merlijn-sebrechts/Splitflaps/documentation/datasheets/schema.png

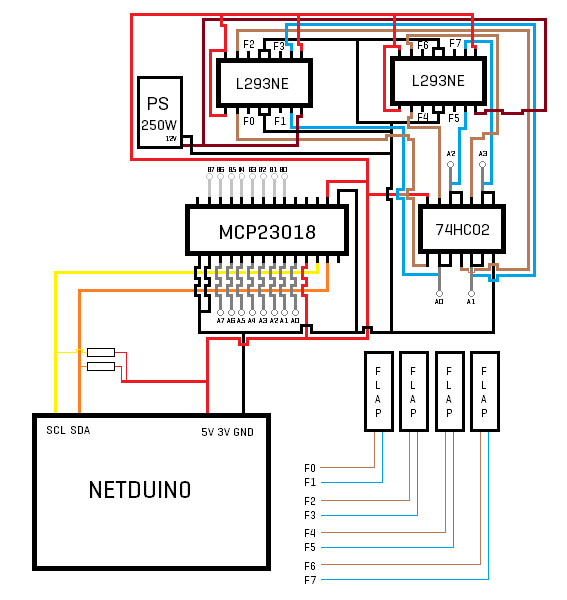
documentation/datasheets/schema.png
