merlijn-sebrechts/Splitflaps/documentation/designs & technical reports/design casing/twitterboard_backplate.jpg

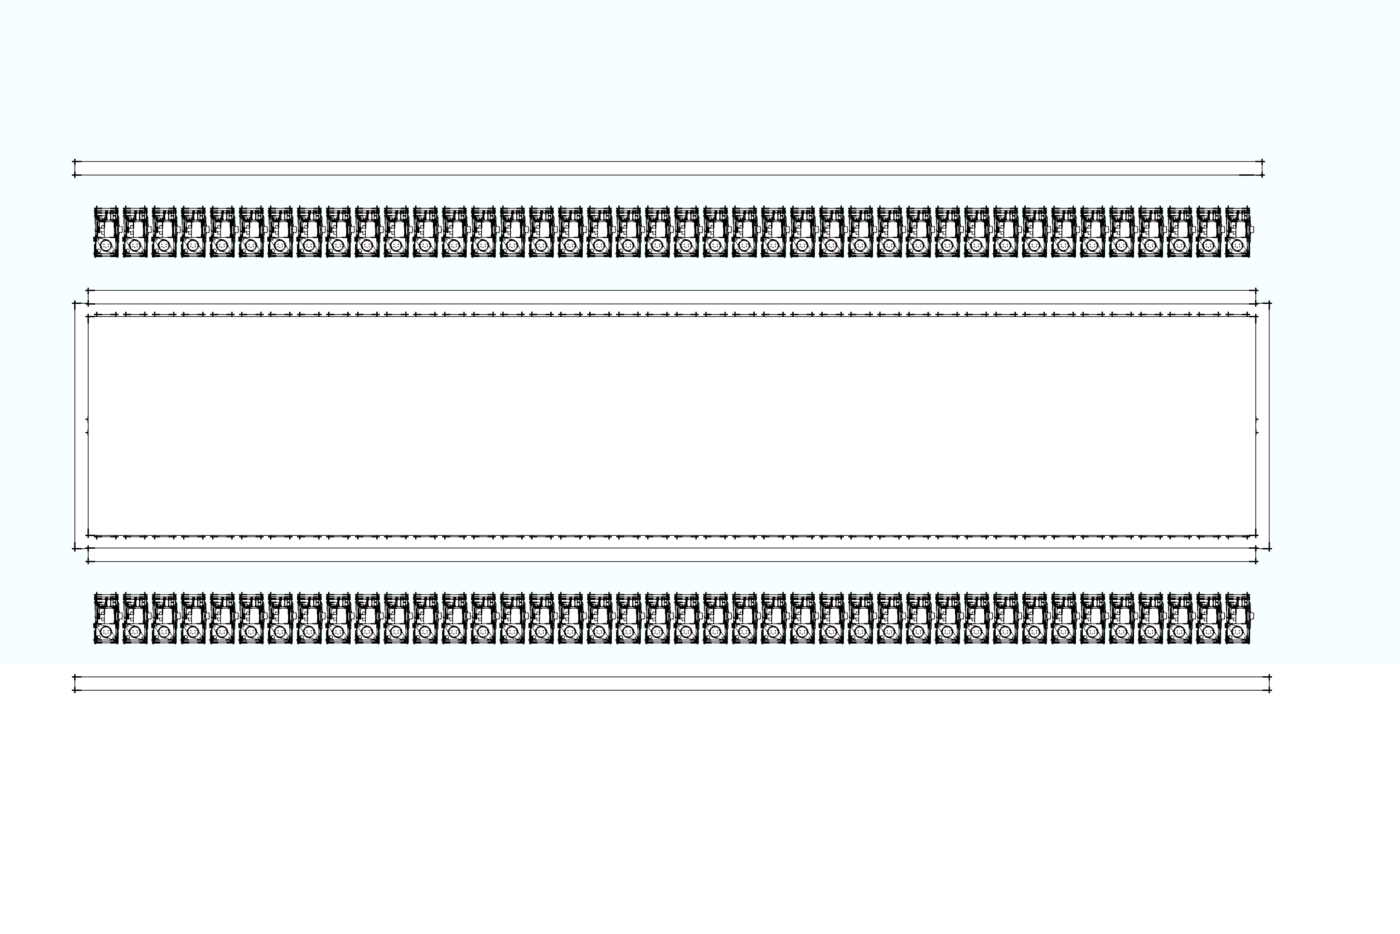
documentation/designs & technical reports/design casing/twitterboard_backplate.jpg
