merlijn-sebrechts/Splitflaps/documentation/designs & technical reports/design casing/twitterboard_elevationwithoutfrontplate.jpg

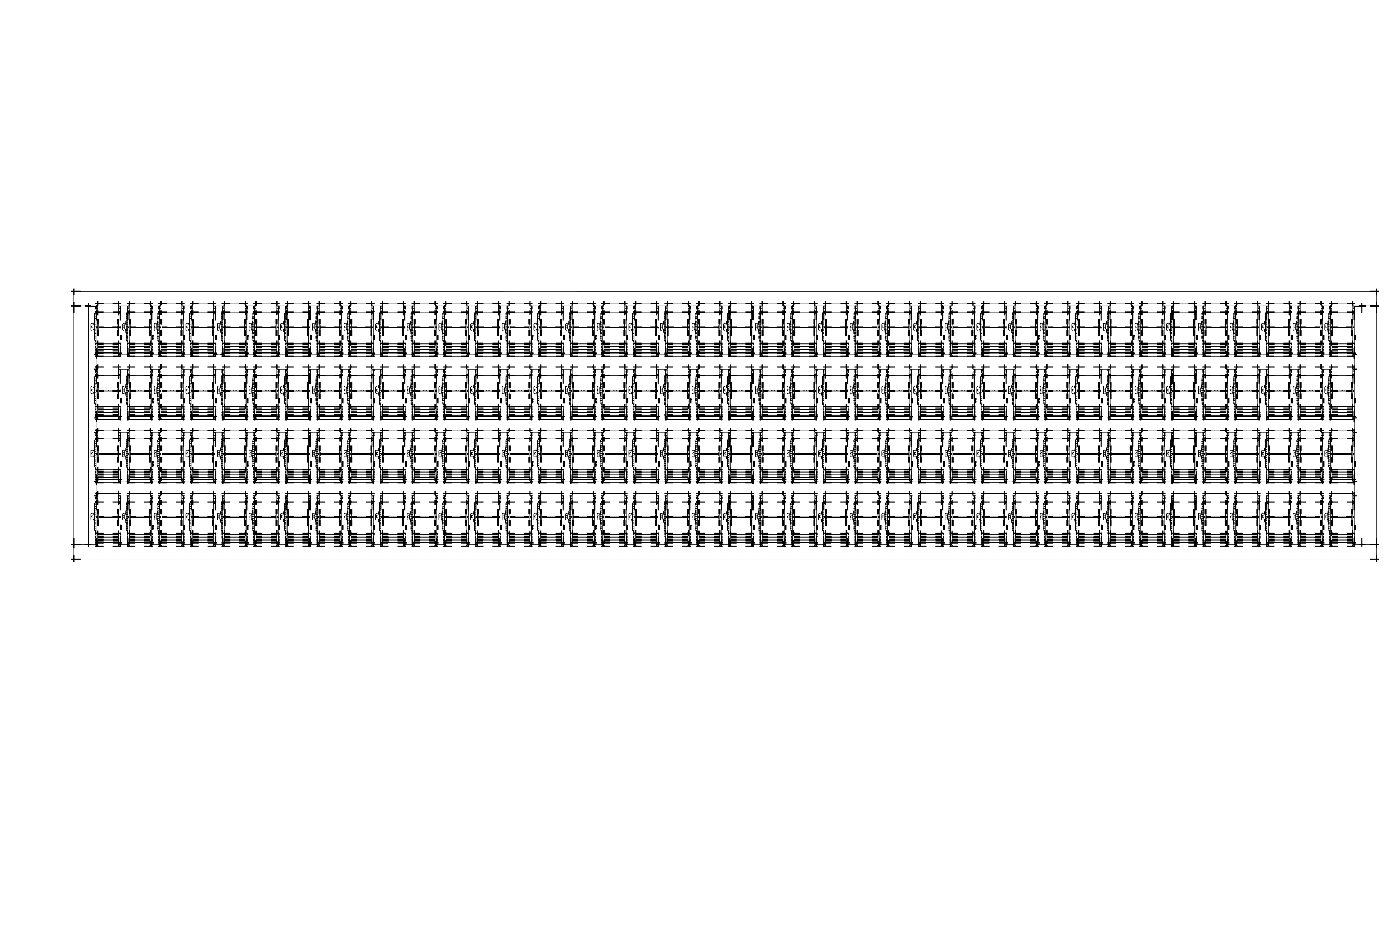
documentation/designs & technical reports/design casing/twitterboard_elevationwithoutfrontplate.jpg
