merlijn-sebrechts/Splitflaps/documentation/designs & technical reports/design casing/twitterboard_frontplate.jpg

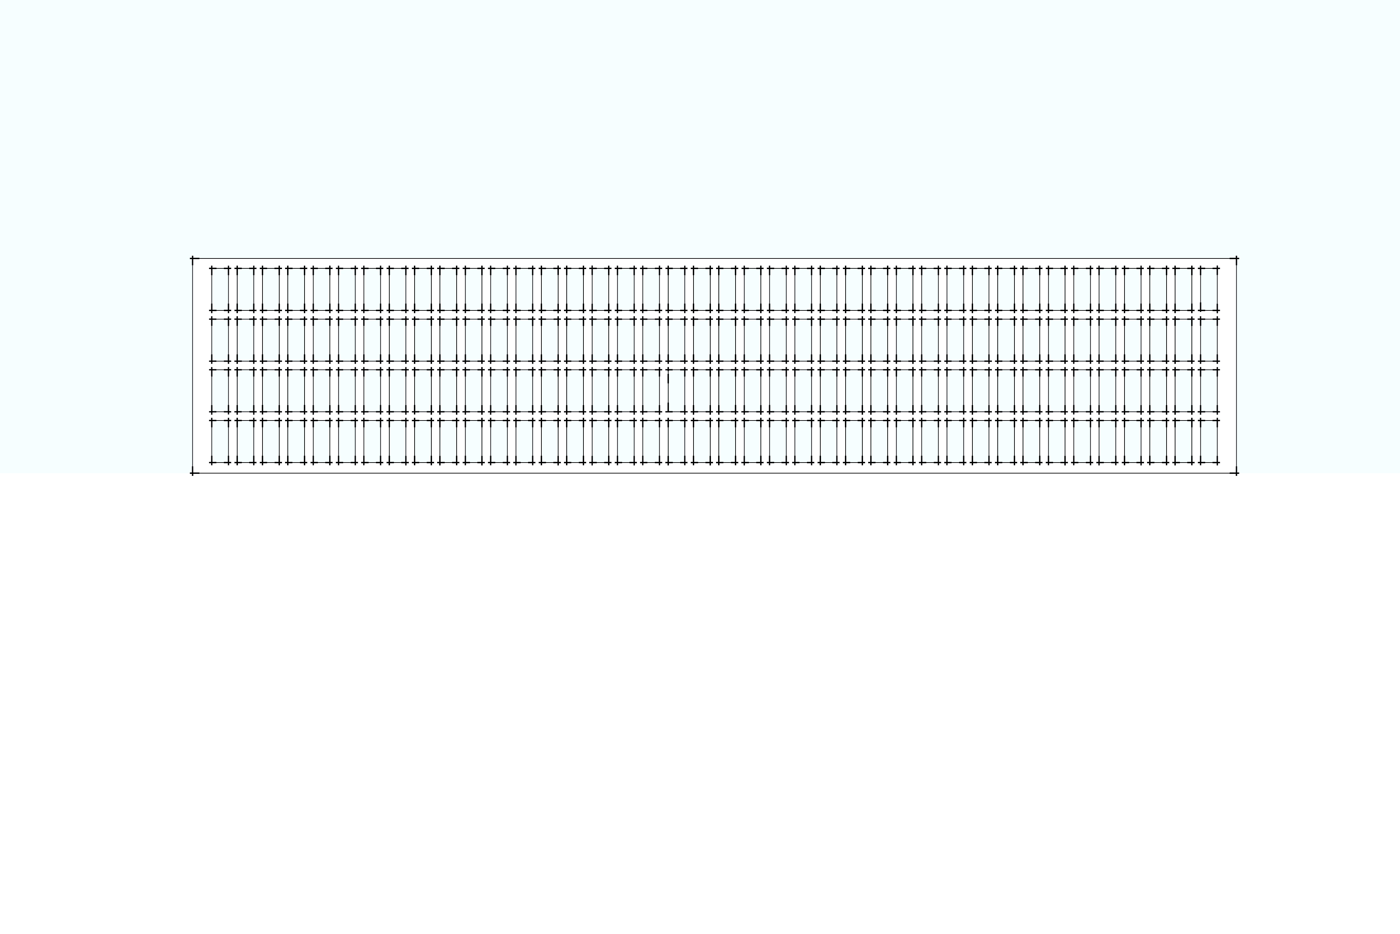
documentation/designs & technical reports/design casing/twitterboard_frontplate.jpg
