merlijn-sebrechts/Splitflaps/documentation/designs & technical reports/design casing/twitterboard_sideelevation.jpg

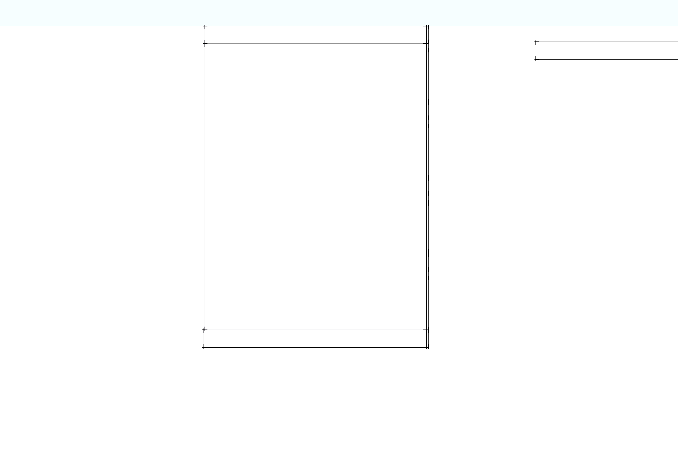
documentation/designs & technical reports/design casing/twitterboard_sideelevation.jpg
