merlijn-sebrechts/Splitflaps/documentation/designs & technical reports/soldeerboard.png

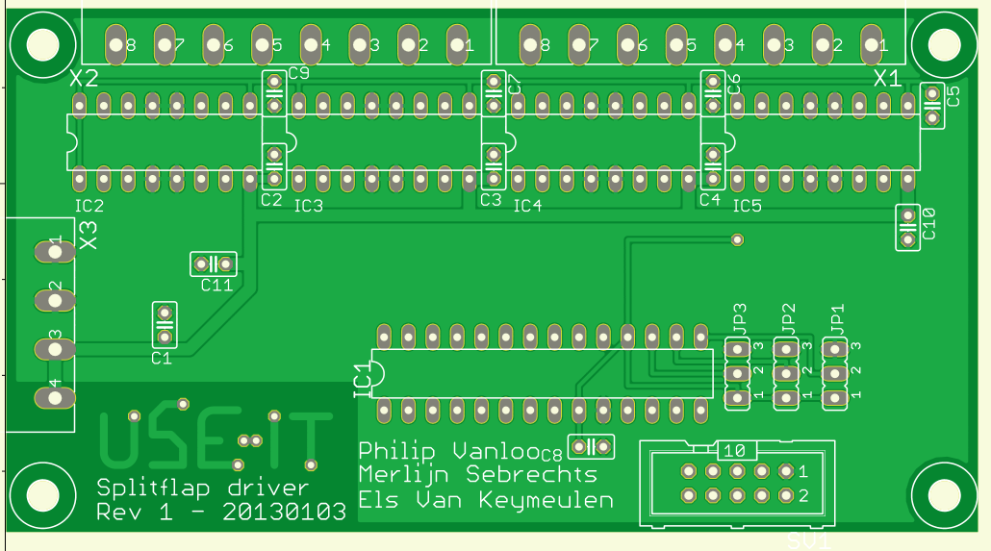
documentation/designs & technical reports/soldeerboard.png
