merlijn-sebrechts/Splitflaps/documentation/designs & technical reports/Sturing van de splitflaps/eendraad klad.jpg

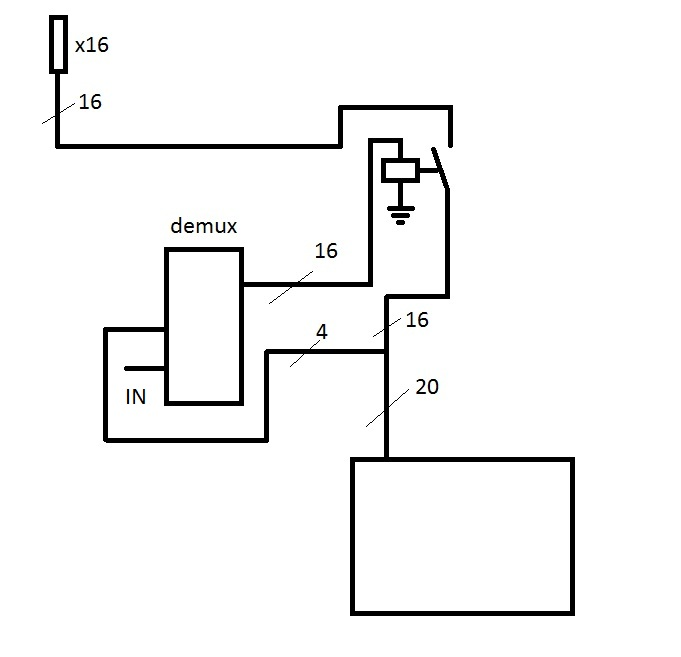
documentation/designs & technical reports/Sturing van de splitflaps/eendraad klad.jpg
