merlijn-sebrechts/Splitflaps/documentation/frontend.png

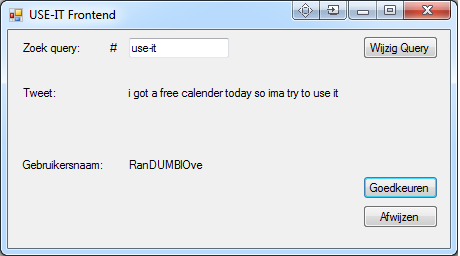
documentation/frontend.png
