merlijn-sebrechts/Splitflaps/documentation/Media/2012-03-01 15.24.06.jpg

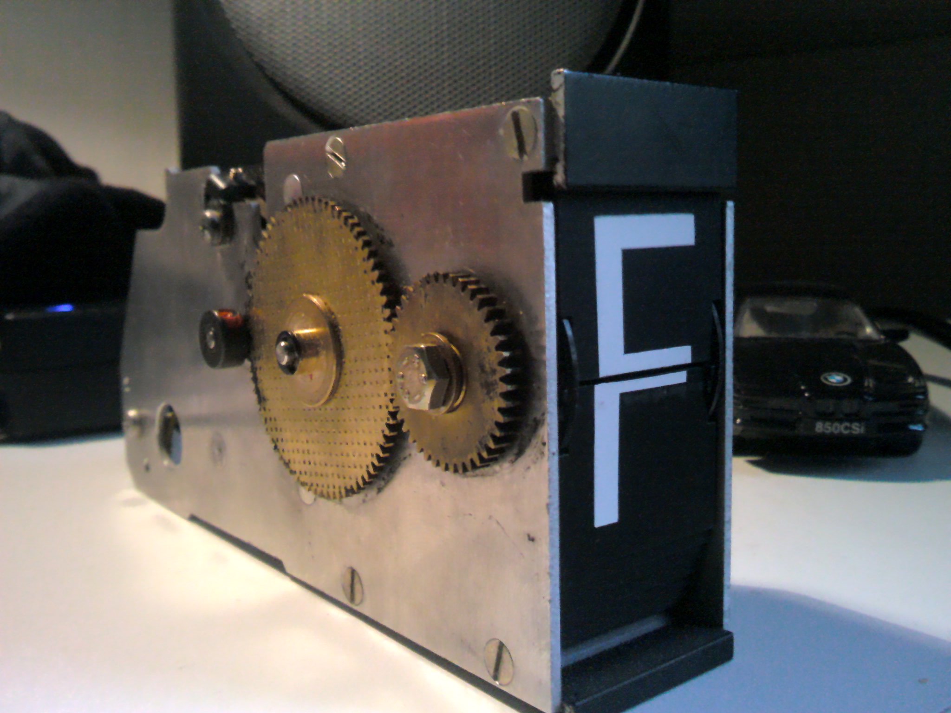
documentation/Media/2012-03-01 15.24.06.jpg
