merlijn-sebrechts/Splitflaps/documentation/Media/2012-03-01 15.25.54.jpg

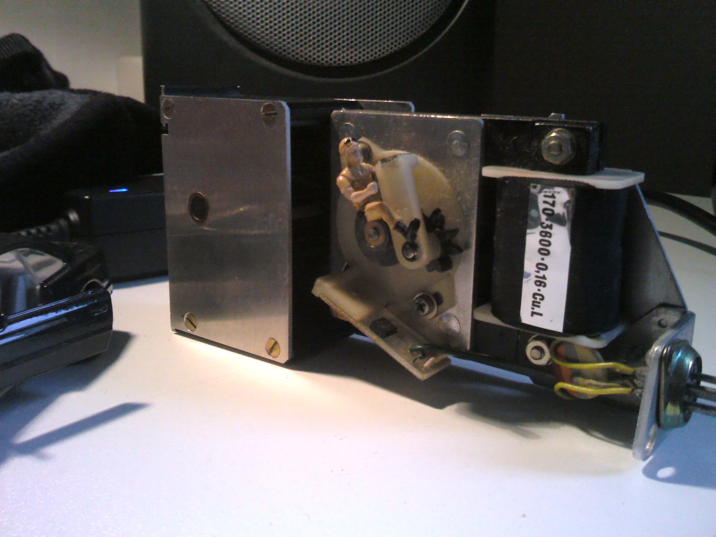
documentation/Media/2012-03-01 15.25.54.jpg
