merlijn-sebrechts/Splitflaps/documentation/Media/2012-03-01 15.26.38.jpg

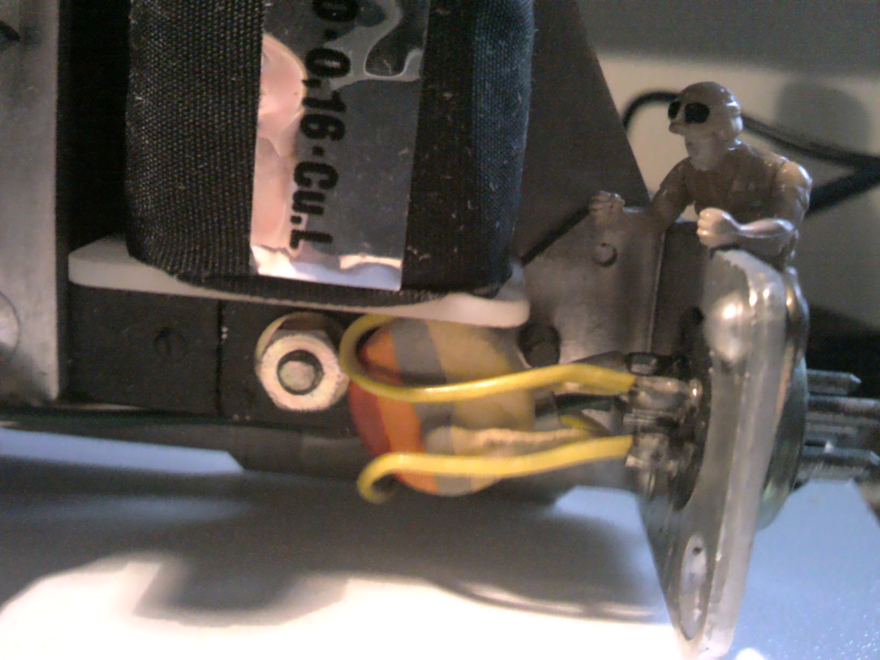
documentation/Media/2012-03-01 15.26.38.jpg
