merlijn-sebrechts/Splitflaps/documentation/Media/2012-03-26 11.21.38.jpg

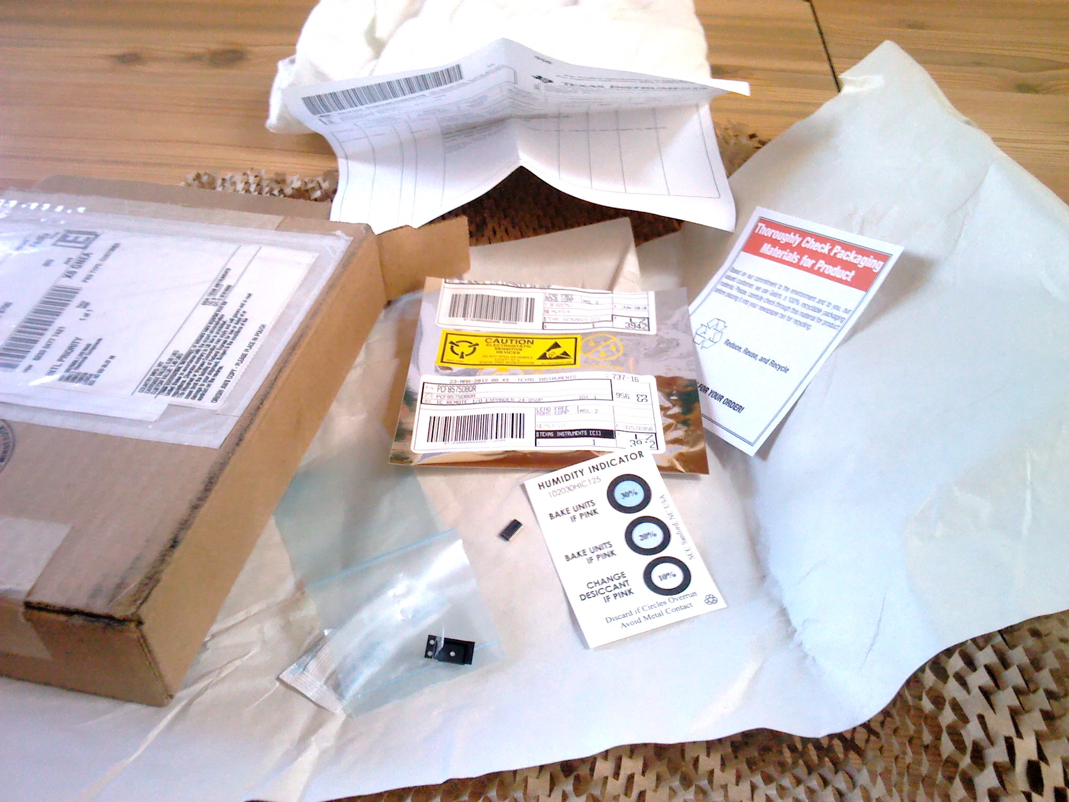
documentation/Media/2012-03-26 11.21.38.jpg
