merlijn-sebrechts/Splitflaps/documentation/Media/2012-05-13 12.06.36.jpg

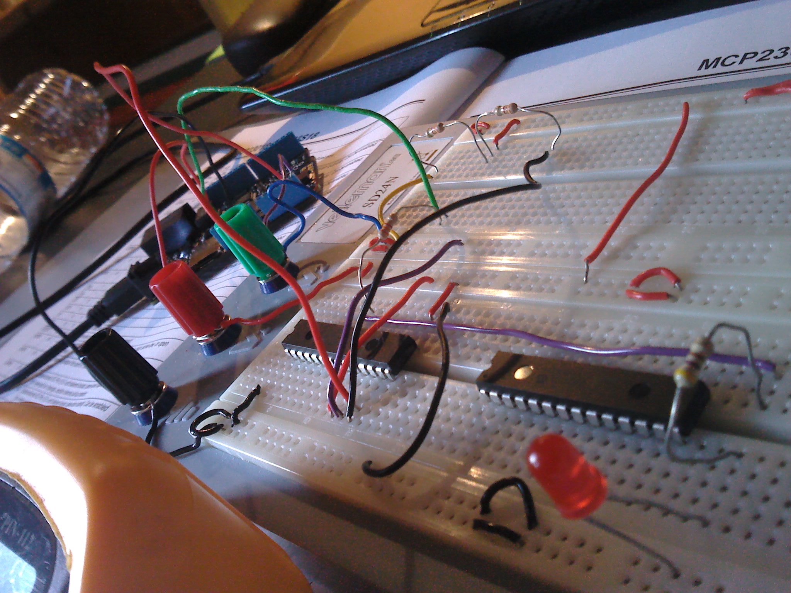
documentation/Media/2012-05-13 12.06.36.jpg
