merlijn-sebrechts/Splitflaps/documentation/Media/2012-05-24 22.02.43.jpg

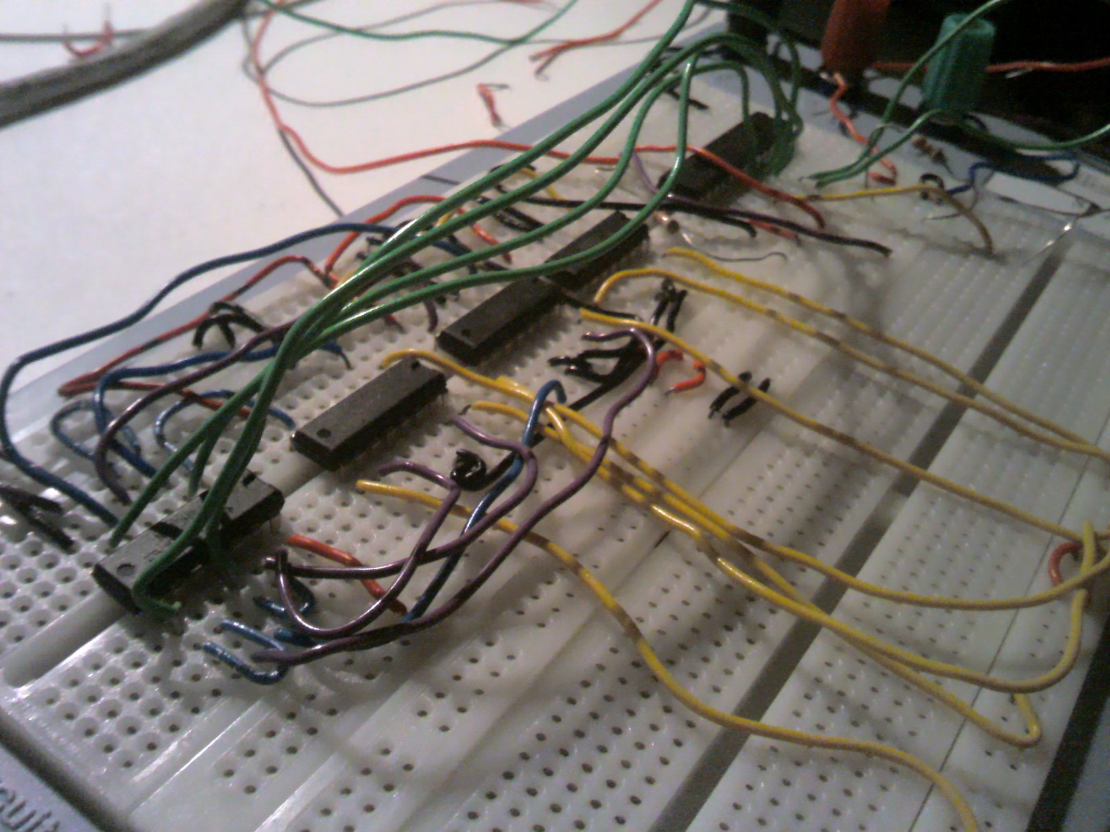
documentation/Media/2012-05-24 22.02.43.jpg
