merlijn-sebrechts/Splitflaps/documentation/Media/2012-10-18 19.46.36.jpg

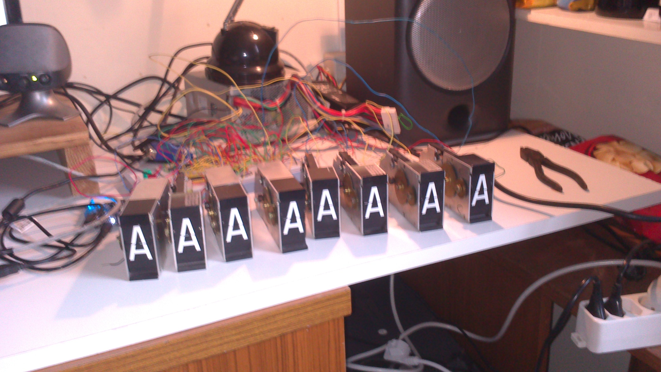
documentation/Media/2012-10-18 19.46.36.jpg
