merlijn-sebrechts/Splitflaps/documentation/Media/2013-10-26 10.34.53.jpg

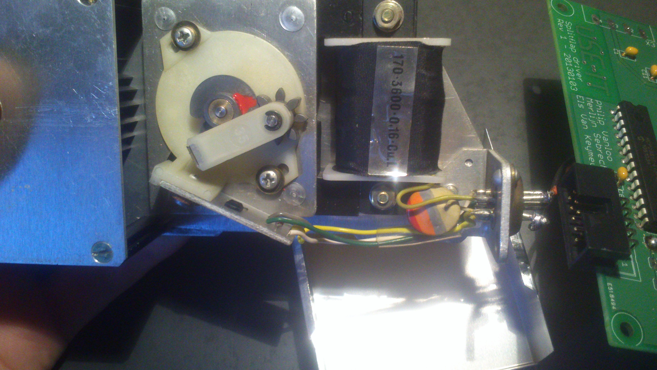
documentation/Media/2013-10-26 10.34.53.jpg
