merlijn-sebrechts/Splitflaps/documentation/Media/2013-10-26 10.35.50.jpg

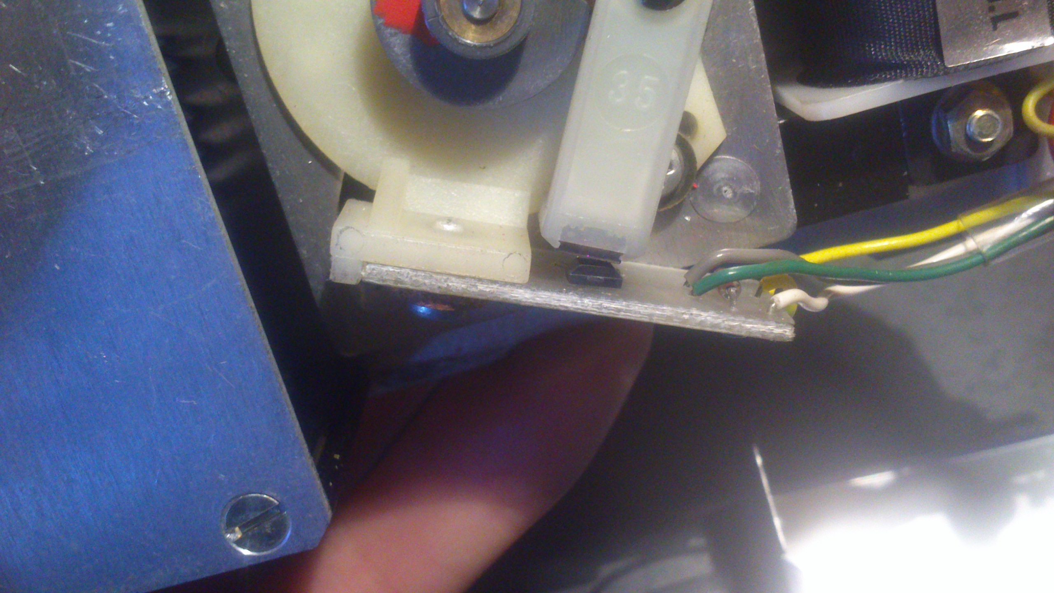
documentation/Media/2013-10-26 10.35.50.jpg
