merlijn-sebrechts/Splitflaps/documentation/Media/2013-10-26 10.36.17.jpg

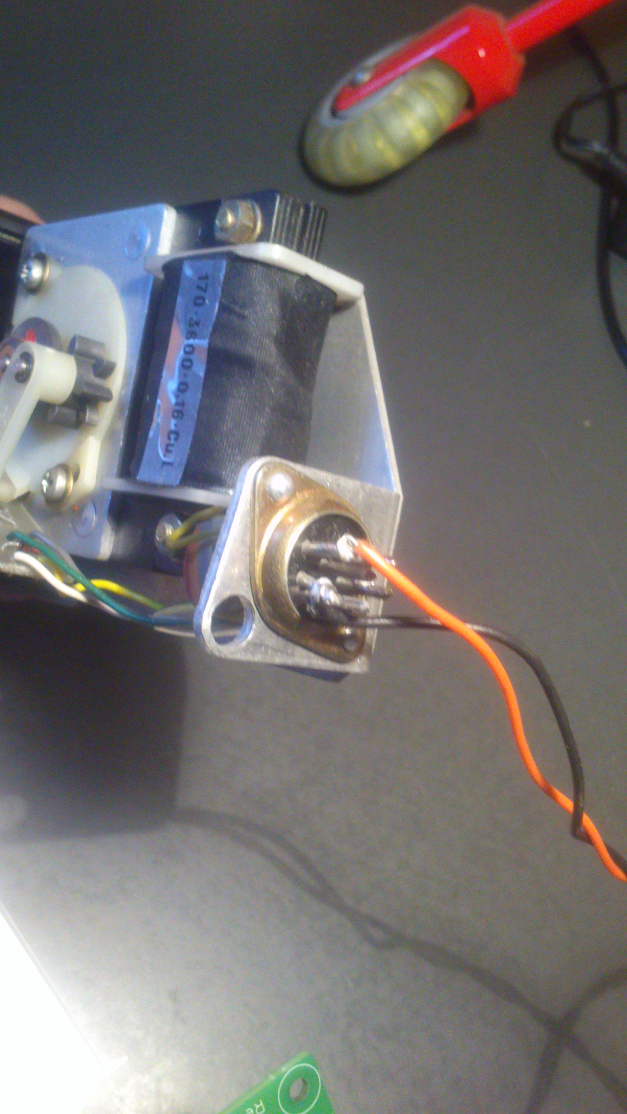
documentation/Media/2013-10-26 10.36.17.jpg
