merlijn-sebrechts/Splitflaps/documentation/Media/2013-10-26 10.39.55.jpg

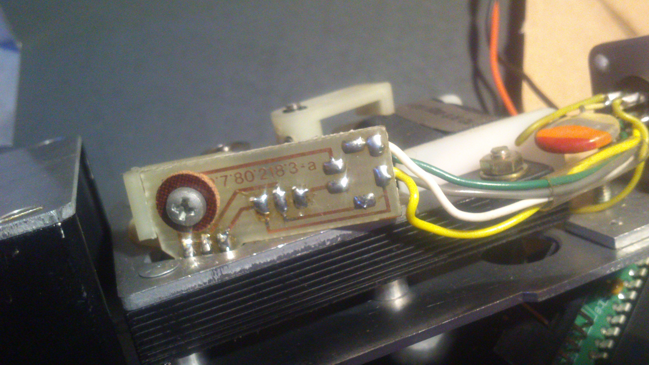
documentation/Media/2013-10-26 10.39.55.jpg
