merlijn-sebrechts/Splitflaps/documentation/Naamloos.png

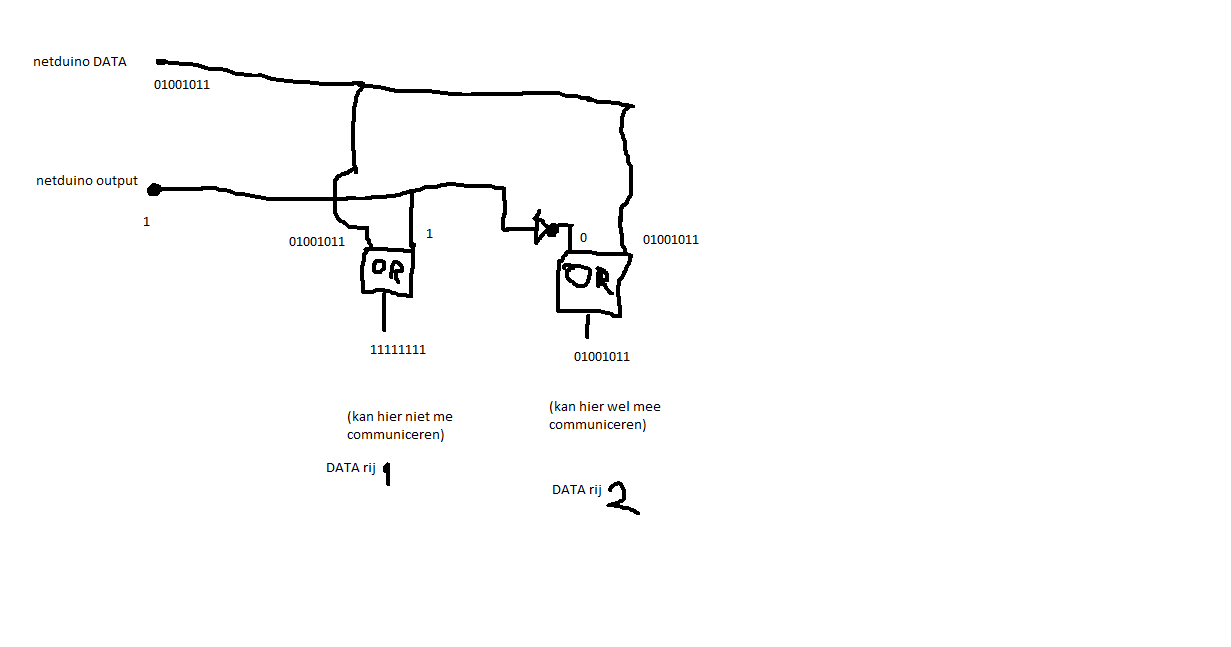
documentation/Naamloos.png
